keith06388/mpptcharger2/Solar_charger/batt.h

/*
 * TinyOLED-Fonts - Fonts for Tiny4kOLED
 * https://github.com/datacute/TinyOLED-Fonts
 * https://github.com/datacute/Tiny4kOLED
 */
/*
 * SSD1306xLED - Drivers for SSD1306 controlled dot matrix OLED/PLED 128x64 displays
 *
 * @created: 2014-08-12
 * @author: Neven Boyanov
 *
 * Source code available at: https://bitbucket.org/tinusaur/ssd1306xled
 *
 */

// ----------------------------------------------------------------------------

#include <avr/pgmspace.h>

// ----------------------------------------------------------------------------

/* Standard ASCII 16x32 font */
const uint8_t ssd1306xled_fontbatt [] PROGMEM = {       

	// @128 '0' (16 pixels wide)
  0xf0, 0xf8, 
  0x38, 0x38, 
  0x38, 0x3e, 
  0x3f, 0x3f, 
  0x3f, 0x3f, 
  0x3e, 0x38, 
  0x38, 0x38, 
  0xf8, 0xf0, 
  0xff, 0xff, 
  0x00, 0x00, 
  0x00, 0x00, 
  0x00, 0x00, 
  0x00, 0x00, 
  0x00, 0x00, 
  0x00, 0x00, 
  0xff, 0xff, 
  0xff, 0xff, 
  0x00, 0x00, 
  0x00, 0x00, 
  0x00, 0x00, 
  0x00, 0x00, 
  0x00, 0x00, 
  0x00, 0x00, 
  0xff, 0xff, 
  0xff, 0xff, 
  0x00, 0x00, 
  0x00, 0x00, 
  0x00, 0x00, 
  0x00, 0x00, 
  0x00, 0x00, 
  0x00, 0x00, 
  0xff, 0xff, 
  0x7f, 0xff, 
  0xe0, 0xe0, 
  0xe0, 0xe0, 
  0xe0, 0xe0, 
  0xe0, 0xe0, 
  0xe0, 0xe0, 
  0xe0, 0xe0, 
  0xff, 0x7f,

	// @192 '1' (16 pixels wide)
  0xf0, 0xf8, 
  0x38, 0x38, 
  0x38, 0x3e, 
  0x3f, 0x3f, 
  0x3f, 0x3f, 
  0x3e, 0x38, 
  0x38, 0x38, 
  0xf8, 0xf0, 
  0xff, 0xff, 
  0x00, 0x00, 
  0x00, 0x00, 
  0x00, 0x00, 
  0x00, 0x00, 
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
  0xff, 0x7f                      

	
};

const DCfont TinyOLED4kfontbatt = {
  (uint8_t *)ssd1306xled_fontbatt,
  16, // character width in pixels
  5, // character height in pages (8 pixels)
  48,53 // ASCII extents
  };

// for backwards compatibility
#define FONTbatt (&TinyOLED4kfontbatt)
